hboyce4/Current_Probe/Photos/20201220_142839.jpg

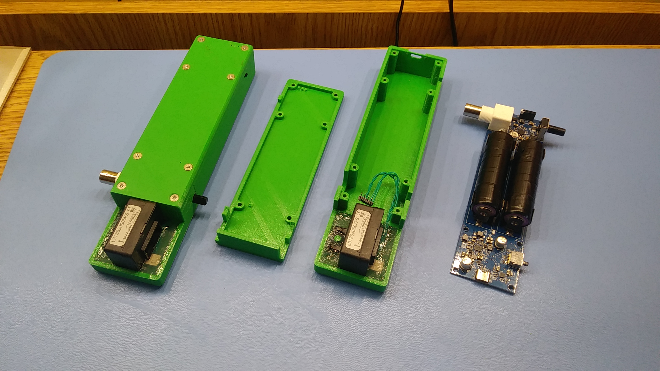
Photos/20201220_142839.jpg
