hboyce4/Current_Probe/Photos/20201220_142855.jpg

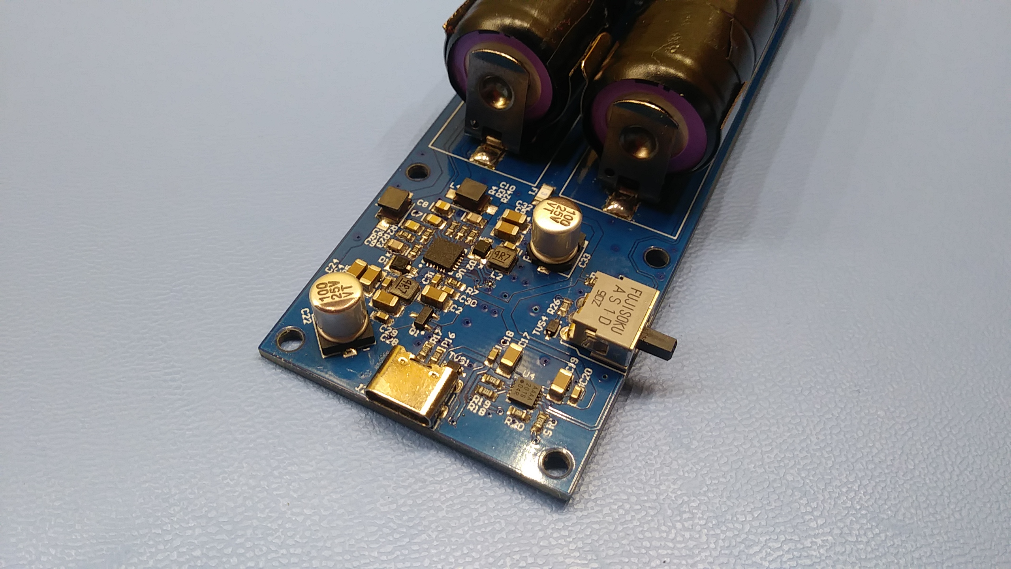
Photos/20201220_142855.jpg
