hboyce4/Current_Probe/Photos/20201220_142910.jpg

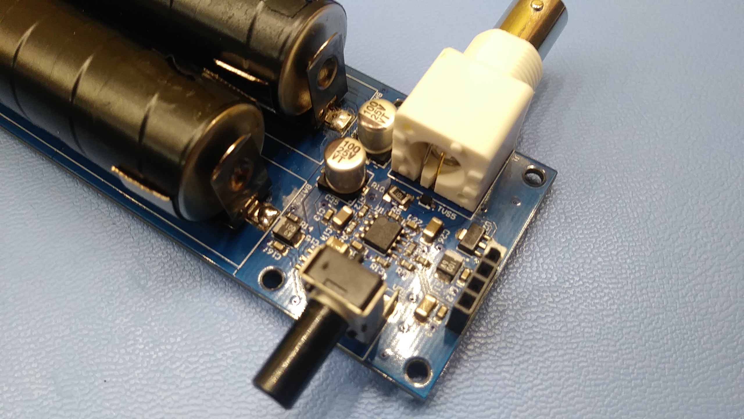
Photos/20201220_142910.jpg
