hboyce4/Current_Probe/Photos/20201220_150028.jpg

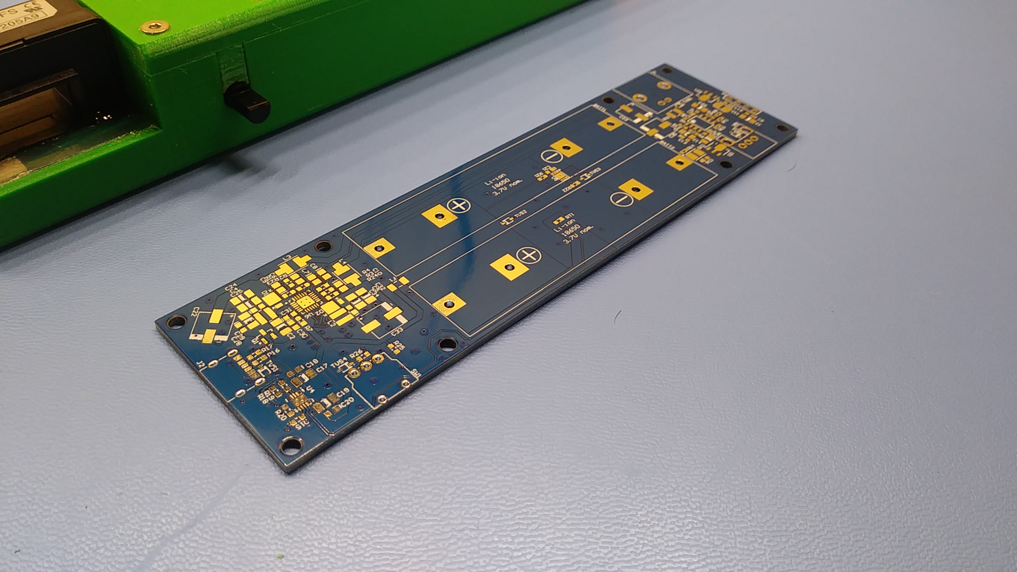
Photos/20201220_150028.jpg
