hboyce4/Current_Probe/Photos/20201220_150035.jpg

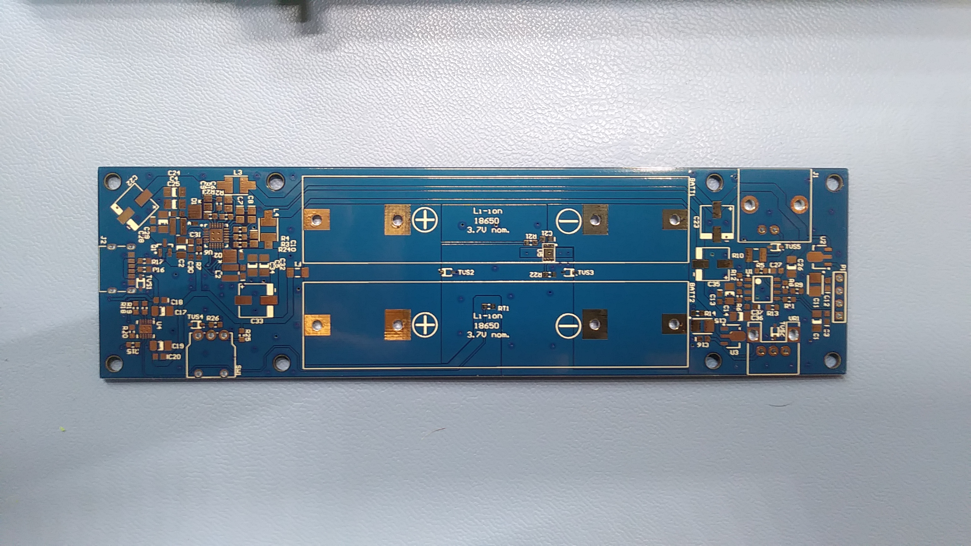
Photos/20201220_150035.jpg
