hboyce4/Current_Probe/Photos/20201220_150125.jpg

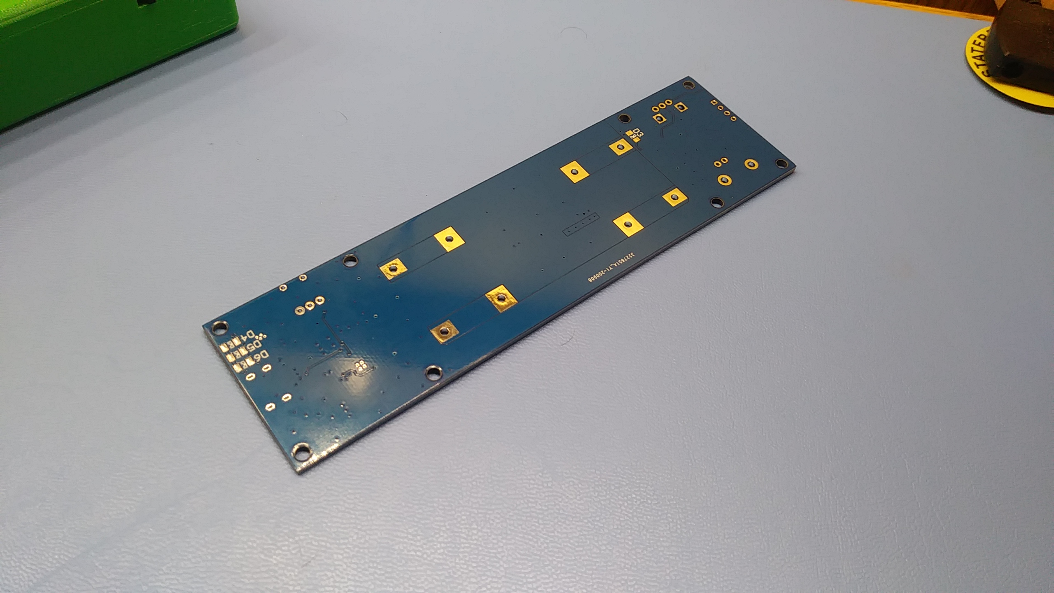
Photos/20201220_150125.jpg
