hboyce4/Current_Probe/Validation/Noise_negative_post_filter.png

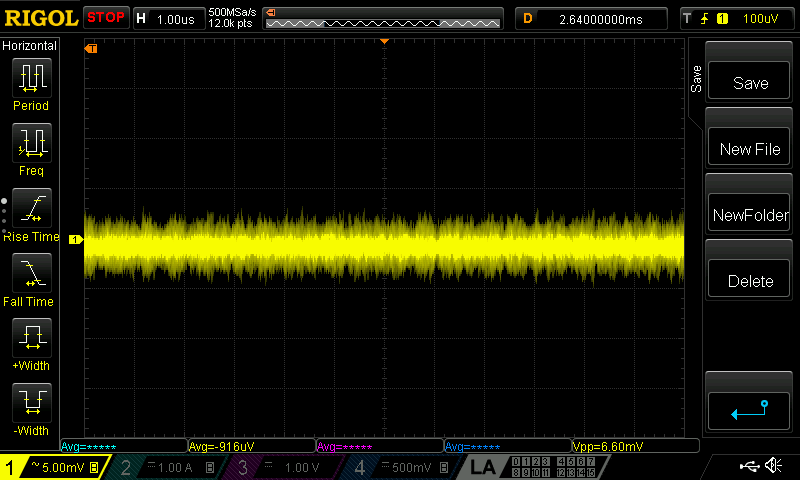
Validation/Noise_negative_post_filter.png
