hboyce4/Current_Probe/Validation/Noise_negative_pre_filter.png

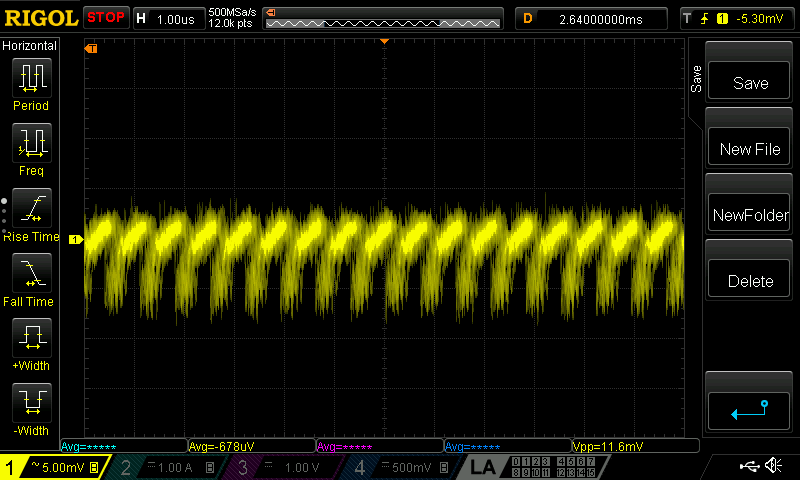
Validation/Noise_negative_pre_filter.png
