hboyce4/Current_Probe/Validation/shunt(yellow)_vs_probe(blue).png

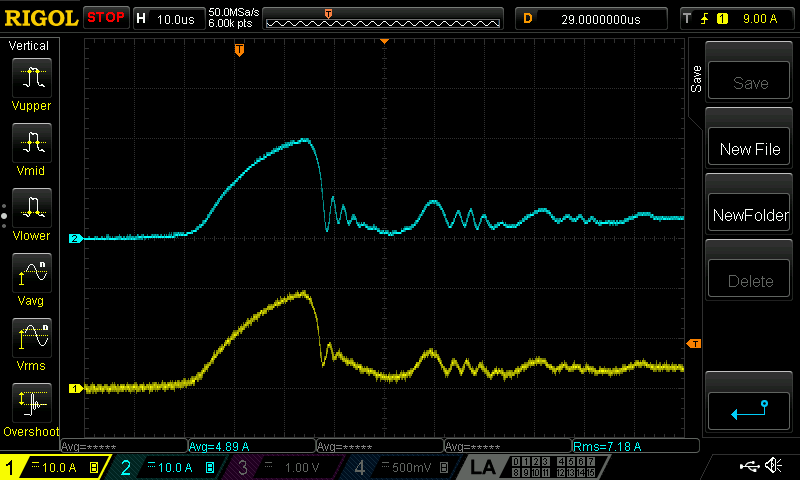
Validation/shunt(yellow)_vs_probe(blue).png
