hboyce4/Current_Probe/Validation/Supplies_rise_time12V_No_Power_saving.png

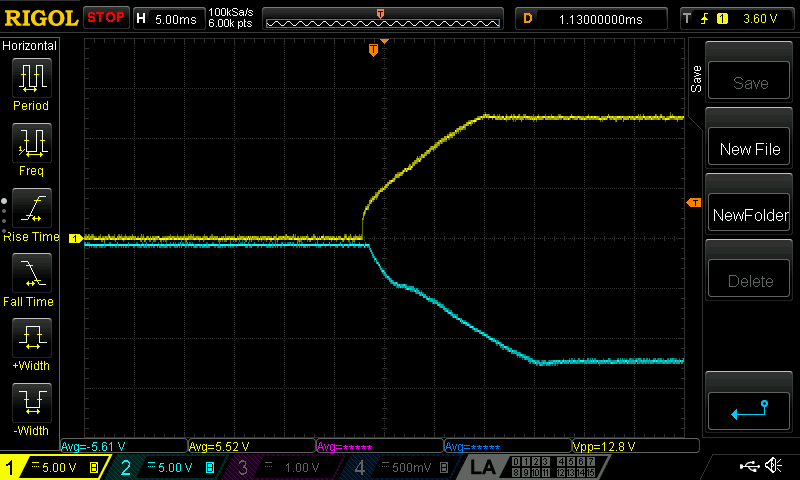
Validation/Supplies_rise_time12V_No_Power_saving.png
